FloEdelmann/bachelor/edel17/Dokumentation/Latex/Titel/erklaerung-lmu.tex

%
% LaTeX-Rahmen für Arbeiten am Lehrstuhl Hegering
%
% Harald Roelle, 2001, 2002
%
% basierend auf Arbeiten von Helmut Reiser, Boris Gruschke und Stephen Heilbronner
%

\newpage

\thispagestyle{empty}

\begin{large}

\vspace*{2cm}

\noindent
Hiermit versichere ich, dass ich die vorliegende Bachelorarbeit
selbständig verfasst und keine anderen als die angegebenen Quellen
und Hilfsmittel verwendet habe.

\vspace{2cm}

\noindent
München, den 27. November 2017

\vspace{3cm}

\hspace*{7cm}%
\dotfill\\
\hspace*{8.5cm}%
\textit{(Unterschrift des Kandidaten)}

\end{large}
