FloEdelmann/bachelor/edel17/Dokumentation/Latex/Bilder/spi-schematic.pdf

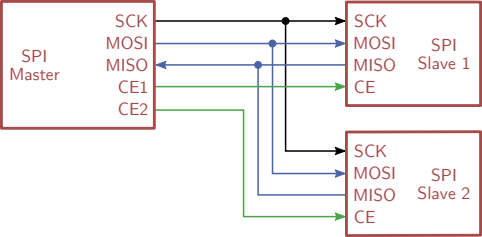
[picture p7: figure]
SPI Master; SCK MOSI MISO CE1 CE2; SPI Slave 1; SCK MOSI MISO CE; SPI Slave 2
