FloEdelmann/bachelor/edel17/Dokumentation/Latex/Bilder/system-design-schematic.pdf

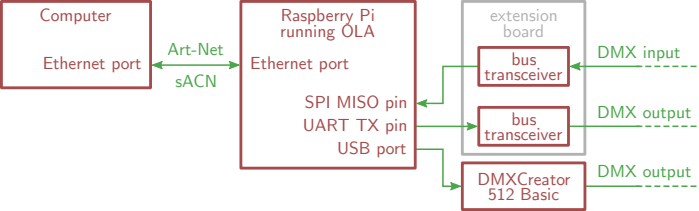
[picture p8: figure]
DMX input; SPI MISO pin UART TX pin; Ethernet port; USB port; Raspberry Pi; running OLA Computer; Art-Net; sACN; bus transceiver; DMXCreator 512 Basic; DMX output; extension board
