FloEdelmann/bachelor/edel17/Dokumentation/Latex/Bilder/xlr-connectors.pdf

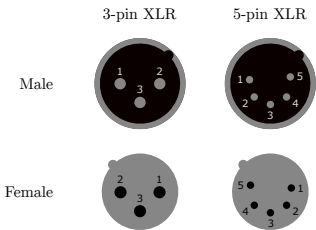
[picture p26: figure]
Male; Female; 3-pin XLR; 5-pin XLR
