FloEdelmann/bachelor/edel17/Dokumentation/Latex/Titel/lmu_siegel.pdf

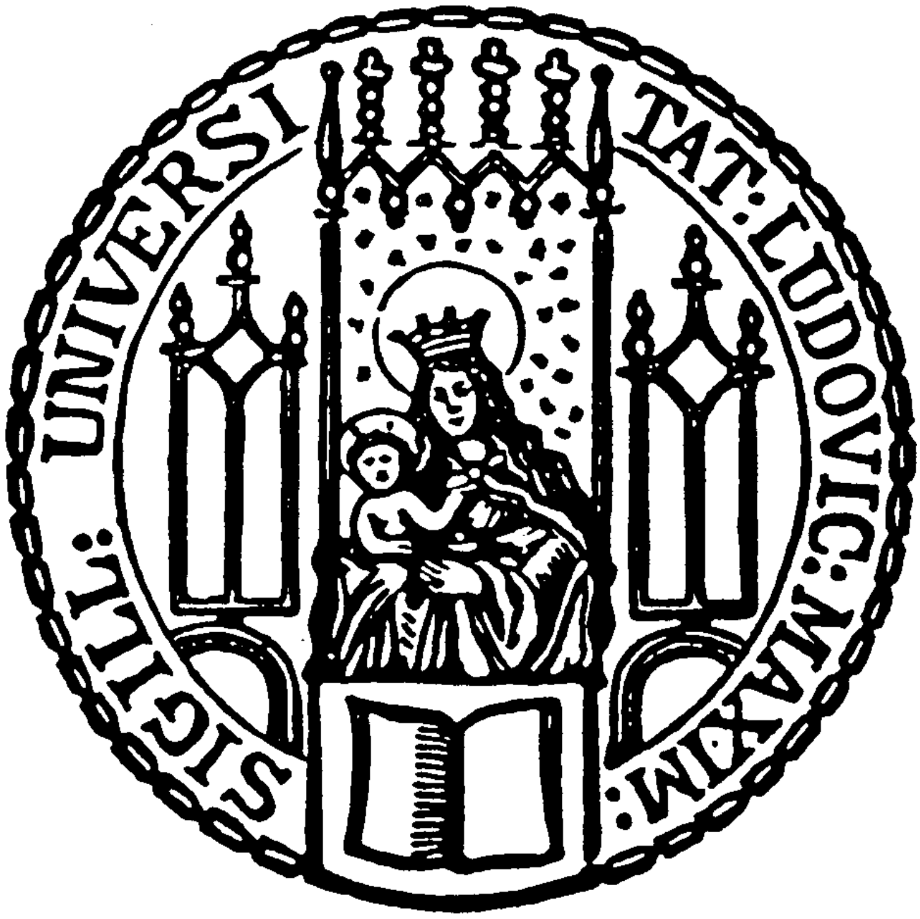
[picture p27: page 1]
