FloEdelmann/bachelor/Bilder/Originale/P1180815.JPG

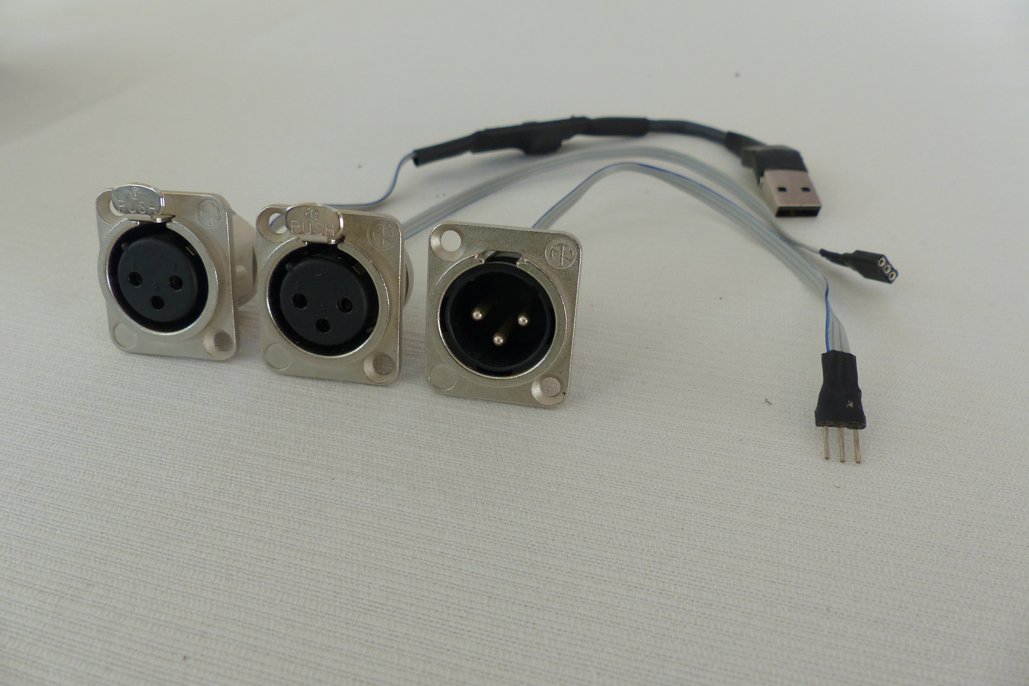
Bilder/Originale/P1180815.JPG
