FloEdelmann/bachelor/Bilder/Originale/P1180841.JPG

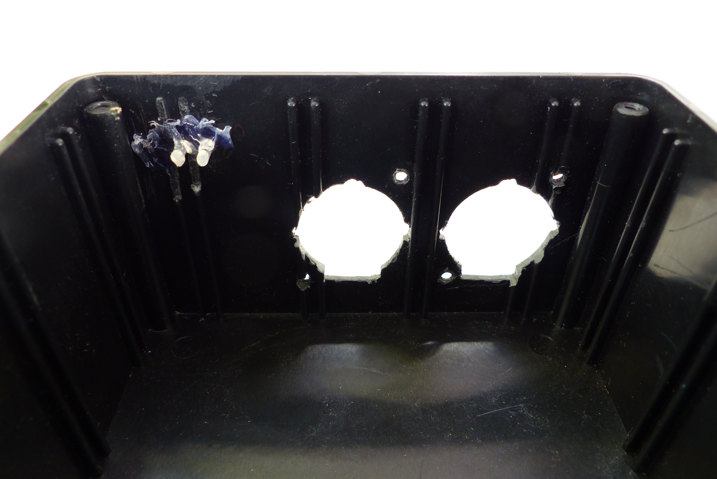
Bilder/Originale/P1180841.JPG
