FloEdelmann/bachelor/eagle/board-bottom.png

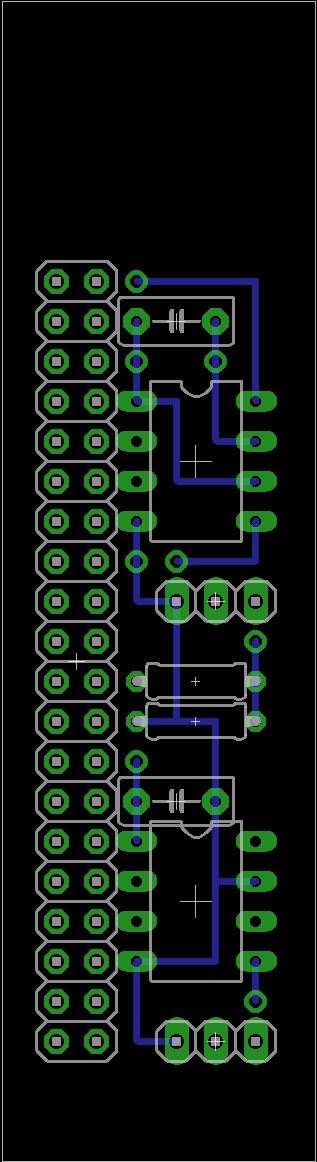
eagle/board-bottom.png
