FloEdelmann/bachelor/eagle/board-top.png

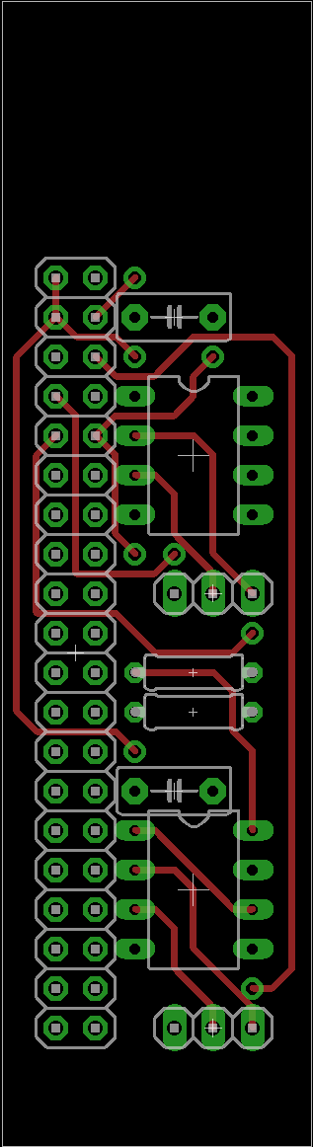
eagle/board-top.png
