FloEdelmann/bachelor/eagle/board.png

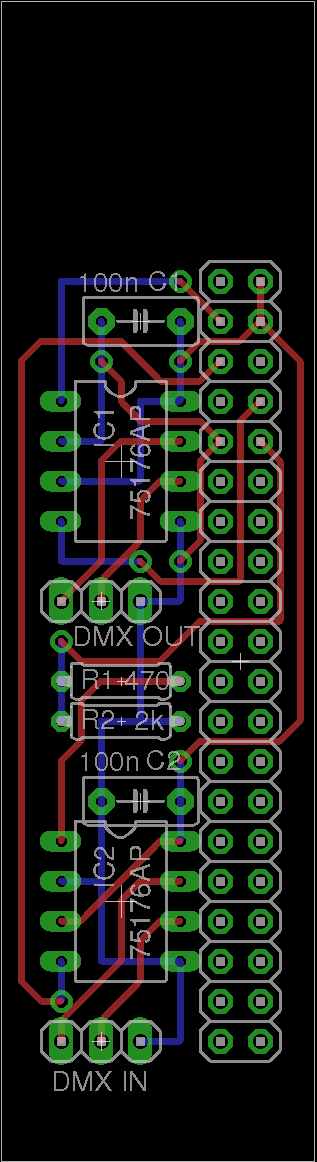
eagle/board.png
