FloEdelmann/bachelor/eagle/eia-485-bus.png

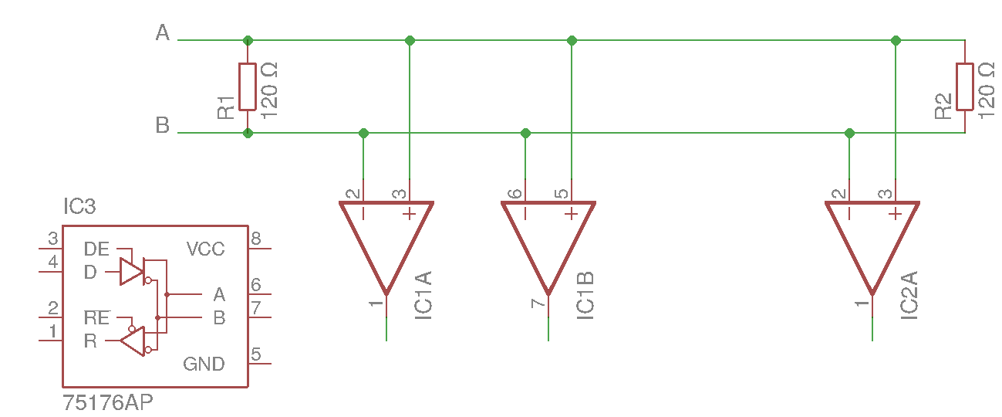
eagle/eia-485-bus.png
