FloEdelmann/bachelor/edel17/Folien/Club_Tropicana_November08.jpg

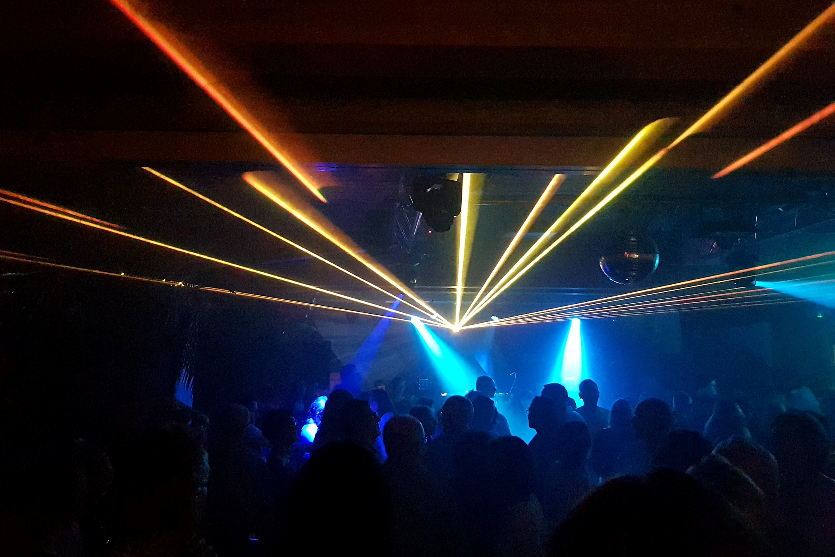
edel17/Folien/Club_Tropicana_November08.jpg
