FloEdelmann/bachelor/edel17/Folien/ola-web-interface.png

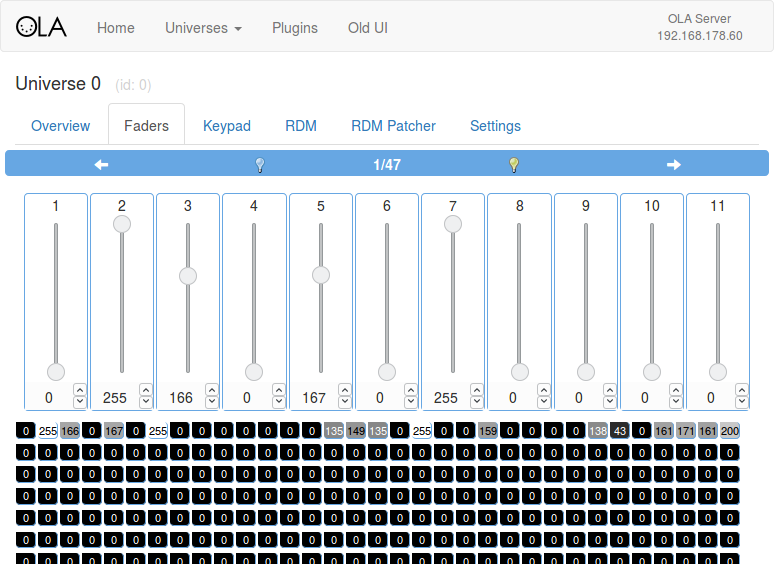
edel17/Folien/ola-web-interface.png
