FloEdelmann/bachelor/edel17/Dokumentation/Latex/Bilder/spi-timing.pdf

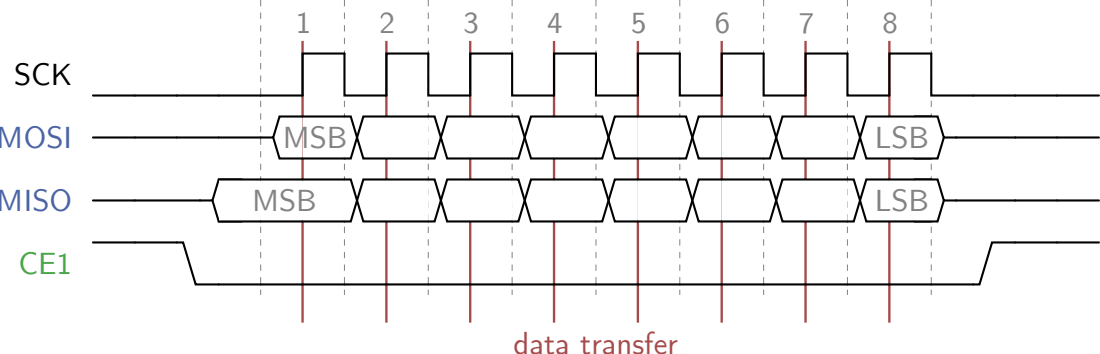
[picture p45: page 1]
SCK; MOSI; MSB; LSB; MISO; data transfer
